cho45/Prosigns/firmware/nlz.h

uint32_t NLZ (uint32_t x) {
	if (x == 0) { return 32; }
	x = x | (x >> 1);
	x = x | (x >> 2);
	x = x | (x >> 4);
	x = x | (x >> 8);
	x = x | (x >>16);
	return 31 - ("\0\1\2\xf\x1d\3\x17\x10\x1e\x1b\4\6\xc\x18\x8\x11\x1f\xe\x1c\x16\x1a\5\xb\7\xd\x15\x19\xa\x14\x9\x13\x12")[0x5763e69U * (x - (x >> 1)) >> 27];
}
