cho45/Prosigns/firmware/morse.h

#include <avr/pgmspace.h>

const uint32_t MORSE_CODES[] PROGMEM = {
	0, // 0 NUL
	0b111010111010111, // 1 SOH => CT / KA
	0, // 2 STH
	0, // 3 ETX
	0b101010111010111, // 4 EOT => SK
	0, // 5 ENQ
	0b10101011101, // 6 ACK => SN
	0, // 7 BEL
	0, // 8 BS
	0, // 9 HT
	0b10111010111, // 10 LF => AA
	0, // 11 VT
	0, // 12 FF
	0, // 13 CR
	0, // 14 SO
	0b1110101011101110111, // 15 SI => DO (WABUN)
	0, // 16 DLE
	0, // 17 DC1
	0, // 18 DC2
	0, // 19 DC3
	0, // 20 DC4
	0, // 21 NAK
	0, // 22 SYN
	0, // 23 ETB
	0, // 24 CAN
	0b1110101010111010111, // 25 EM => BK
	0b111010111011101, // 26 SUB => KN
	0b111010111010101110101, // 27 ESC => CL
	0, // 28 FS
	0, // 29 GS
	0, // 30 RS
	0, // 31 US
	0, // 32 " "
	0b1110101110101110111, // 33 "!"
	0b101110101011101, // 34 """
	0, // 35 "#"
	0b10101011101010111, // 36 "$"
	0, // 37 "%"
	0b10111010101, // 38 "&" AS
	0b1011101110111011101, // 39 "'"
	0b111010111011101, // 40 "("
	0b1110101110111010111, // 41 ")"
	0, // 42 "*"
	0b1011101011101, // 43 "+"
	0b1110111010101110111, // 44 ","
	0b111010101010111, // 45 "-"
	0b10111010111010111, // 46 "."
	0b1110101011101, // 47 "/"
	0b1110111011101110111, // 48 "0"
	0b10111011101110111, // 49 "1"
	0b101011101110111, // 50 "2"
	0b1010101110111, // 51 "3"
	0b10101010111, // 52 "4"
	0b101010101, // 53 "5"
	0b11101010101, // 54 "6"
	0b1110111010101, // 55 "7"
	0b111011101110101, // 56 "8"
	0b11101110111011101, // 57 "9"
	0b11101110111010101, // 58 ":"
	0b11101011101011101, // 59 ";"
	0, // 60 "<"
	0b1110101010111, // 61 "=" BT
	0, // 62 ">"
	0b101011101110101, // 63 "?"
	0b10111011101011101, // 64 "@"
	0b10111, // 65 "A"
	0b111010101, // 66 "B"
	0b11101011101, // 67 "C"
	0b1110101, // 68 "D"
	0b1, // 69 "E"
	0b101011101, // 70 "F"
	0b111011101, // 71 "G"
	0b1010101, // 72 "H"
	0b101, // 73 "I"
	0b1011101110111, // 74 "J"
	0b111010111, // 75 "K"
	0b101110101, // 76 "L"
	0b1110111, // 77 "M"
	0b11101, // 78 "N"
	0b11101110111, // 79 "O"
	0b10111011101, // 80 "P"
	0b1110111010111, // 81 "Q"
	0b1011101, // 82 "R"
	0b10101, // 83 "S"
	0b111, // 84 "T"
	0b1010111, // 85 "U"
	0b101010111, // 86 "V"
	0b101110111, // 87 "W"
	0b11101010111, // 88 "X"
	0b1110101110111, // 89 "Y"
	0b11101110101, // 90 "Z"
	0, // 91 "["
	0, // 92 "\"
	0, // 93 "]"
	0, // 94 "^"
	0b10101110111010111, // 95 "_"
	0, // 96 "`"
	0, // 97 "a"
	0, // 98 "b"
	0, // 99 "c"
	0, // 100 "d"
	0, // 101 "e"
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
	0b101010101010101, // 127 DEL
};
